mpaiva/gol-cam/.plans/session-2026-06-04.md

# Session Summary — 2026-06-04

## Prompts (in order)
1. *"create a plan to add the cam calibration to the display"*
2. *"implement option b"*
3. *"update the session summary"*

## What shipped

### Plan: cam calibration on the HMI display
- **`abe38cf`** — `.plans/cam-calibration-on-hmi.md`. Three UX
  options (A: enhanced side-status pill; B: calibration overlay
  covering the score area; C: full calibration snapshot with JPEG
  decode), with cost/risk and a recommended phasing A → B → defer C.

### Option B: full calibration overlay on the HMI
Implemented over 4 commits as user-feedback drove the UI from a
small panel up to a full-screen modal that repaints the placar
cleanly on dismiss:

- **`1b36d56`** — Option B baseline. `CamState` gained
  `motionTh`, `colorTh`, `calContrast`, `hasCalSnap`, and a 40-byte
  `calMsg`. New `extractStringField()` helper mirrors the existing
  `extractIntField` / `extractBoolField` JSON parsers. New
  `CalOverlay` struct + state machine
  (`RUNNING → RESULT_OK/FAIL → OFF`). `drawCalOverlay()` renders
  title / live `calMsg` / 3-stop progress bar / Cancelar button. Cam
  state transitions (`1 → 0`) trigger the RESULT phase. `ACT_CAL_CANCEL`
  resets the cam and collapses the overlay. Touch hit-test swallows
  taps under the overlay; only Cancelar fires (returns `-2`,
  routed to `ACT_CAL_CANCEL`). 70/70 integration tests still passed.

- **`cb9fe2e`** — polish: `calMsg` buffer bumped 40 → 64 bytes (the
  cam's full failure message is ~61 chars), added a raise-time
  snapshot of `calMsg` plus a 500 ms min-age gate so a stale FAILED
  message from the previous attempt no longer flips the overlay to
  RESULT_FAIL on frame 1 (this was the entire "neither change took"
  user feedback), and rewrote the panel as solid white fillRect (no
  rounded corners) with strong blue text — eliminates corner
  bleed-through. Result phase keeps green/red title colour-coding;
  Cancelar keeps red bg + white text.

- **`a33cb2e`** — overlay is now full-screen (800 × 480) and all
  underlay redraws are gated by `!overlayActive()`. Without this,
  `pollCam`'s `dirtyButtons` flag would punch the green START rect
  through the white overlay (the screenshot that showed "START
  visible inside the white panel"). Same gate on the touch-release
  drawButton(prev/btn) in `serviceTouch()`. Title bumped to text
  size 4 for the bigger canvas, layout reflowed around the new
  dimensions, dismiss path sets `dirtyHeader` too since the header
  is now also under the overlay.

- **`dcb85b7`** — dismiss path now calls `renderFull()` directly
  instead of relying on the loop's per-flag redraws. The loop's
  `dirtyButtons` handler is hard-coded to repaint only button index
  5 (START, the only one whose label changes via pollCam), so
  dismissing the full-screen overlay left the other 7 placar
  buttons white-on-white. Both dismiss paths (state-machine
  auto-dismiss after 3 s and `ACT_CAL_CANCEL`) now do a full
  fillScreen + drawHeader + drawScoreDigits + drawButtons (all 8)
  + drawSideStatus. Added a forward declaration for `renderFull()`.

### Calibration plan updated
- **`abe38cf`** + (next: needs Option B status update). Mark Option
  B as **DONE** in `.plans/cam-calibration-on-hmi.md`.

## What did NOT ship (yet)
- **Option A** (the cheaper enhanced side-status pill from the
  same plan). Skipped because the user wanted Option B directly,
  and Option B effectively subsumes A — the live `calMsg`,
  thresholds, and result feedback all show up in the overlay.
- **Option C** (full calibration snapshot via JPEG decode).
  Deferred per the original plan.
- **The HMI WebServer-lockup follow-up** from 2026-06-03 was
  closed as part of yesterday's session (`77ec6ec` ported to
  `esp_http_server`, `651b116` made the test runner keep-alive
  per host). Verified 70/70 today as a regression check after the
  baseline overlay landed.

## Bugs discovered + fixed during user-testing
| # | Symptom | Root cause | Fix |
|---|---|---|---|
| 1 | `calMsg` truncated to "Place dadi" | 40-byte buffer too small | Bump to 64 bytes (cb9fe2e) |
| 2 | Title said "Calibrando" with a FAILED message under it | Cam stays in state=1 for a beat after writing the failure to calMsg | Detect FAILED/FALHOU prefix in calMsg and flip to RESULT_FAIL early (cb9fe2e) |
| 3 | Early-fail flipped on frame 1 | Stale calMsg from the previous attempt was already present | Snapshot calMsg at CAL-tap time + 500 ms min-age gate (cb9fe2e) |
| 4 | "Memory issue with the display" — dark overlay had artifacts | Rounded corners exposed underlying score view through transparent radii | Solid white fillRect + blue text, no rounded corners (cb9fe2e) |
| 5 | Green START leaking through white overlay | `dirtyButtons` from pollCam triggered `drawButton(5)` while overlay was up | Gate the underlay redraws by `!overlayActive()` (a33cb2e) |
| 6 | User expected full-screen overlay | Overlay was 780 × 335, header + side-status visible in black around it | Switch to 800 × 480 + gate dirtyHeader + dirtyStatus too (a33cb2e) |
| 7 | Placar came back "stripped" after overlay dismissed | Loop's dirtyButtons handler only redraws button index 5 (START) | Call `renderFull()` directly in both dismiss paths (dcb85b7) |

## Verification
- `python3 tests/integration/test_system.py` → **70/70 green** after
  the Option B baseline (1b36d56). Not re-run after every polish
  commit since the polish was UI-only (no REST surface changed).
- User-visual confirmation at each iteration via `/remote-control`
  screenshots.

## Commit list this session
- `abe38cf` — docs: cam-calibration plan
- `1b36d56` — hmi: calibration overlay (Option B baseline)
- `cb9fe2e` — hmi: overlay polish (64-byte buffer, raise-time gate, white panel)
- `a33cb2e` — hmi: full-screen overlay + all-layer gating
- `dcb85b7` — hmi: renderFull() on dismiss

All pushed to `origin/master`. Tree clean. Branches in sync.

## Pickup list for next session

1. **Test the calibration overlay during an actual partida.**
   The flow has been verified statically — tap CAL A, see overlay,
   see calMsg/progress, RESULT phase, dismiss to clean placar. Real
   referee usage during a match will surface anything we missed:
   - Does the operator hit Cancelar before they meant to?
   - Is the 3 s RESULT phase the right duration?
   - Do they want to see the cam's calMsg in the FAIL result page
     (currently we show the generic "Sem dadinho detectado /
     Posicione e toque CAL novamente" instead)?
2. **Camera B intermittent dropouts.** Still happening from
   yesterday's session — cam B at `192.168.40.91` goes offline
   periodically. Either a hardware issue (power, cable) or a
   firmware-level WiFi/HTTP server problem. Test by leaving cam B
   running for an hour and watching `/status` via curl. If it
   reliably drops, capture serial during the drop.
3. **Retire the LED MAX7219 placar.** With the HMI fully working
   as the placar + operator surface, the LED placar is no longer
   needed. Physically power it down OR keep it as a parallel mirror
   (set its IP to something other than `.89`).
4. **Option A from the cal-calibration plan is now obsolete** —
   the side-status pill enhancement was redundant with the overlay.
   Could either remove the Option A description from the plan or
   leave it as historical context. Trivial cleanup.

## How to pick up cold
- `git log --oneline -10` shows all commits.
- The cal-overlay implementation lives in
  `src_hmi/main.cpp`:
  - `CamState` extensions: lines ~273-292
  - `CalOverlay` struct + constants: lines ~340-370
  - `extractStringField()`: lines ~395-410
  - `runAction()` cases for CAL_A / CAL_B / CAL_CANCEL: ~620-680
  - `drawCalOverlay()` + `updateCalOverlay()`: lines ~880-1000
  - `hitTest()` overlay route + `serviceTouch()` press-feedback
    gating: ~1010-1130
  - Main loop dirty-flag gates: ~1340-1360
  - Overlay paint at end of loop: ~1365-1370
- `curl http://192.168.40.89/debug/touch` returns chip diagnostic
  state any time.
- `python3 tests/integration/test_system.py` runs the 70-check
  REST suite. Persistent keep-alive client (651b116) means
  re-running back-to-back is safe.
- HMI serial is on `/dev/cu.usbserial-110` (was `-10` earlier in
  the session; port renumbered when the cable was replugged).

---

## Continued — 2026-06-04 (later in the day)

### Prompt
*"the screens and buttons work, but the calibration is not as
successful as the legacy method. is this because of limiting
processing power of the display board?"*

The honest answer: no — calibration runs entirely on the camera, the
HMI just sends the trigger and shows the result. The user's perceived
quality drop comes from operating blind: the cam dashboard shows a
live MJPEG with ROI overlay, the HMI showed nothing about what the cam
was actually seeing. Took two follow-up requests from there
("implement option c" → ship the static cal-snapshot preview; *"scope
[live MJPEG] as a follow-up plan"* → write the plan).

### Option C: cam-snapshot preview in the overlay (SHIPPED, commit `ae41369`)
Pulls the cam's `/cal-snapshot` JPEG into a PSRAM buffer, decodes
with TJpg_Decoder, renders into a 320×240 region of the calibration
overlay. Operator can now see what the cam was looking at and
diagnose failures ("dark image, no edges found → cam needs more
light") at a glance.

Tech notes:
- Added `bodmer/TJpg_Decoder@^1.1.0` to platformio.ini for crowpanel_hmi
  env.
- 32 KB PSRAM buffer alloc'd once at boot via `ps_malloc`; observed
  JPEG sizes are ~2 KB but the cam can grow larger for textured
  scenes.
- TJpgDec callback receives ABSOLUTE screen coords (already offset
  by what was passed to `drawJpg(SNAP_X, SNAP_Y)`), so the callback
  passes `x, y` straight to `gfx->draw16bitRGBBitmap` without
  further adjustment. The first version of the callback was
  double-adding `SNAP_X + x`, putting pixels off-screen.
- Two-fetch trigger: once on overlay raise (instant preview of
  previous attempt's frame), once on state-transition to RESULT
  (refresh to THIS attempt's frame). Result phase auto-dismiss
  extended from 3 s to 6 s so the second fetch has time to
  complete and the user actually sees the new frame.
- Anti-flicker: `snapVersion` counter bumps on each successful
  fetch; `drawCalOverlay` only re-decodes the JPEG when the
  version changes since last paint. Without this gate, every
  `dirtyOverlay` tick (caused by polling, state changes, etc.)
  was re-fillRect-ing and re-decoding the snap area.
- The full-screen white background fill that opens
  `drawCalOverlay` is now done in four strips AROUND the snap
  area instead of one rect through it. Otherwise the version
  gate would refuse to re-decode, leaving the snap area white
  between fetches.

Bug journey along the way:
| # | Symptom | Root cause | Fix |
|---|---|---|---|
| 1 | Snapshot fetch never logged | User wasn't tapping CAL during my serial-capture windows; bash `echo` prompts are invisible to the user | Use AskUserQuestion to coordinate tap timing; capture in background and read the saved log after |
| 2 | `TJpgDec.drawJpg returned 1` but no image visible | Callback was double-adding SNAP_X/Y → pixels at (560+, 300+), off-screen | Pass `x, y` straight from the callback to gfx without offset |
| 3 | Image renders for first fetch, "(carregando…)" persists for second | State-transition request sets `calSnapReady=false`, drawCalOverlay paints placeholder over the image, second fetch never re-paints because result phase auto-dismissed before fetch completed | Extend result-phase timeout from 3 s to 6 s |
| 4 | Image renders but flickers heavily | Every `dirtyOverlay` tick re-fillRect'd + re-decoded the snap area, even when the JPEG hadn't changed | Add `snapVersion` counter + version-gated decode in drawCalOverlay |
| 5 | Less flicker but still some | Top-of-`drawCalOverlay` fillRect was clearing the snap area on every call; version-gate then refused to re-decode | Replace the fullscreen fillRect with 4 strips that leave the snap area untouched |

### Plan: live MJPEG preview as a follow-up (NOT SHIPPED, doc only)
- **`1416e1f`** — `.plans/live-stream-preview.md`. Three scope levels
  (A: live during overlay only — recommended; B: always-on main view;
  C: two-up side-by-side). Level A breakdown lists 5 sub-tasks each
  ~50 LOC, leans entirely on the already-shipped TJpgDec +
  version-gated redraw plumbing. Only the feed source changes from
  one-shot `/cal-snapshot` to continuous `/stream` MJPEG at 5 fps.
- Plan honestly says ESP32-S3 can't run a browser to mirror the cam's
  HTML/JS dashboard directly — the live-stream + native-button
  hybrid is the realistic answer to "can we access the cam UI from
  the display?"

### Final commit list (this session, full)
- `abe38cf` — docs: cam-calibration plan
- `1b36d56` — hmi: calibration overlay (Option B baseline)
- `cb9fe2e` — hmi: overlay polish
- `a33cb2e` — hmi: full-screen overlay + all-layer gating
- `dcb85b7` — hmi: renderFull() on dismiss
- `43923b5` — docs: earlier session summary + mark B done
- `ae41369` — hmi: cal-snapshot preview (Option C)
- `1416e1f` — docs: live-stream follow-up plan

All pushed to `origin/master`. Tree clean.

### Updated pickup list

1. **Implement Level A of `.plans/live-stream-preview.md`** — live
   MJPEG preview during the calibration overlay. Builds on top of
   the existing TJpgDec + version-gated decode plumbing; only the
   feed source changes from one-shot `/cal-snapshot` to continuous
   `/stream` at 5 fps. Closes the blind-calibration UX gap that
   was the originating concern.
2. **Camera B intermittent dropouts.** Still open from yesterday.
3. **Retire the LED MAX7219 placar.** Still applicable.
4. **Test the full overlay+snapshot flow during an actual partida.**
   The static snapshot covers the diagnostic case ("why did cal
   fail?") but not the positioning case ("is the dadinho in
   frame?"). Level A's live preview will cover positioning. Wait
   to do both real-partida tests until Level A ships.
5. **Residual snap-area flicker.** User mentioned brief flicker
   even after the version gate + 4-strip fill. Acceptable for now
   but a cached RGB565 framebuffer (~150 KB in PSRAM) would let
   us blit the decoded frame instead of re-decoding, eliminating
   the flicker entirely. Worth doing as part of Level A when we
   touch this code anyway.

### Updated "how to pick up cold"
Same as before, plus:
- TJpg_Decoder code paths in `src_hmi/main.cpp`:
  - JPEG buffer + state globals: ~lines 360-380
  - `fetchCalSnapshot()`: ~lines 730-790
  - `calSnapTjpgOutput()` (TJpgDec callback): ~lines 800-810
  - `requestCalSnapshot()` helper: ~lines 1380-1395
  - Worker integration in `workerTask()`: ~lines 1320-1355
  - Render block inside `drawCalOverlay()` with version-gate:
    ~lines 940-975
- TJpgDec lib pinned at `bodmer/TJpg_Decoder@^1.1.0` in
  `platformio.ini`.
- The 4-strip background fill at the top of `drawCalOverlay`
  preserves the snap area on each repaint — be careful not to
  re-introduce a fullscreen fillRect.
