mpaiva/gol-cam/.plans/session-2026-06-03-gt911.md

# Session Plan -- 2026-06-03 (resumed from 2026-05-26)

## Prompt
"add an explicit GT911 init sequence" — after the touch panel on the
CrowPanel HMI stopped registering touches entirely (chip alive on I²C
but config-version reg reads 0xFF and status reg stays 0x00).

## Context (what we knew going in)
- HMI board has been promoted from a passive placar mirror to the
  full-featured placar (cameras push goals to it; on-screen referee
  buttons A+/A-/B+/B- + CAL A / START / RESET / CAL B all map to local
  REST handlers).
- Touch was working at one point (RESET button responded), then went
  totally dead after the debounce thresholds were tightened.
- Symptom diagnosis: chip responds to product-ID query (`"911?"`,
  firmware `0x1060`) but config-version register (`0x8047`) reads
  `0xFF` and status register (`0x814E`) is permanently `0x00`. The
  chip has no factory config burned in, so it refuses to scan.

## Things tried that did NOT work
1. **Soft reset (command 0x02).** No effect — chip stayed in same
   no-scan state.
2. **Factory restore (command 0x05).** *Worse* — this command isn't in
   every GT911 firmware revision, and the unit responded by locking up
   its I²C bus. Every subsequent `requestFrom()` returned `Error -1`
   until power cycle. Code path has been reverted.

## What is on the chip right now (commit `4309e69`)
Inline `gt911` driver in `src_hmi/main.cpp`:

1. Probes product ID + firmware version (diagnostic).
2. Reads config version. If `0xFF` or `< 0x42`, writes a verified
   185-byte 800×480 single-touch config blob lifted from Beken's
   `armino` SDK (`middleware/driver/tp/tp_gt911.c`, the `#else`
   branch). Then writes `1` to `0x8100` to commit.
3. Puts command register in normal scan mode (`0`).
4. Clears status byte so the first touch produces a fresh "ready"
   event.
5. Polling loop reads status every ~loop iteration; on bit 7 set,
   reads 7-byte point 1 record and decodes X/Y.

The chunked-write helper (`writeRegs`) splits the 185-byte payload
into 16-byte transactions because Wire's default 128-byte buffer
can't hold the whole thing in one go.

## What to verify next session
1. **Did the config write take?** Plug in HMI, watch serial monitor
   (`pio device monitor -e crowpanel_hmi`). Expect:
   ```
   [gt911] product_id = "911?"
   [gt911] firmware = 0x1060
   [gt911] config version = 0xFF
   [gt911] no valid config — writing fallback blob
   [gt911] writing 800x480 config blob (Beken/armino, ver 0x42)
   [gt911] post-write config version = 0x42 (want 0x42)
   [gt911] init complete, polling enabled
   ```
   If `post-write config version` reads `0x42`, the chip accepted the
   config and should now scan. Touch any button — `[gt911] status=...`
   diagnostic prints every 500 polls should show non-zero values, and
   button-press handlers should fire.

2. **If I²C is still locked up from cmd 0x05:** unplug for >5 seconds
   to fully drain the panel's 3V3 rail, then replug. GT911 will reset
   to its default state.

3. **If config writes but touches still don't fire:** the
   drive/sense thresholds in the Beken blob were tuned for *their*
   800×480 panel, not the Elecrow DIS07050H. Touches may register but
   only at very high pressure, or the chip may keep reporting `status
   = 0x00` because the sensing threshold is too high. Path forward
   then is to capture the chip's behaviour via Goodix's Windows
   tuning tool, or try alternative config blobs (LovyanGFX / TouchGFX
   demos have a few).

## Tertiary follow-ups (queued, not blocking)
- **Retire the LED placar entirely.** The MAX7219 board still gets
  pushed to as a parallel mirror because the camera firmwares haven't
  been re-pointed at the HMI IP. Once touch works, change
  `SCOREBOARD_IP` on both cameras from `.89` (LED placar) to the
  HMI's IP, and unplug the LED placar.
- **Hardware reset pin.** If we ever find which GPIO on the CrowPanel
  is wired to the GT911 RST line, we can do a clean reset on each
  boot and avoid relying on "config version probe" heuristics. The
  Elecrow wiki schematic suggests GPIO 38 might be RST but it's
  unconfirmed.
- **Test suite.** `tests/integration/test_system.py` (70 checks)
  currently passes for placar + cameras. There's no touch-coverage
  test because the HMI exposes touches only via UI side effects, not
  REST. Could add a `/debug/touchcount` endpoint that returns
  `pollCount` + `touchCount` for assertions.

## Commits this session
- `1d4feb4` — hmi: explicit GT911 init sequence (probe id,
  normal-scan, log cfg ver)
- `4309e69` — hmi: write GT911 800x480 config blob when chip ships
  with blank NVRAM

## Open question for the user
Touch behaviour needs to be eyeballed on the hardware — it can't be
verified from this side. The user's next confirmation determines
whether the config-write fixed it or whether we need to chase the
RST-pin or alternate-blob paths.

---

## Update: config-write attempt confirmed FAILED at chip level (later in session)

After flashing the config-blob writer, the user said "buttons aren't
working". Pyserial-based serial capture revealed:

```
[gt911] product_id = "911?"
[gt911] firmware = 0x1060
[gt911] boot config version = 0xFF
[gt911] no valid config — writing fallback blob
[gt911] writing 800x480 config blob (Beken/armino, ver 0x42)
[gt911] post-write pre-commit readback: 42 20 03 E0 01 01 3D 00
[gt911] post-commit config version = 0xFF (want 0x42)   ← REVERTED
[gt911] init complete, polling enabled
[gt911] status=0x00 (poll #500)
[gt911] status=0x00 (poll #1000)
...
```

What we learned:
- **Writes succeed** — chip accepts and stores our 185 bytes in config
  RAM. Pre-commit readback shows `42 20 03 E0 01 01 3D 00` (the
  first 8 bytes of the Beken blob) exactly. Bus is healthy.
- **Commit silently fails** — `0x8100 ← 1` (and `0x8101 ← 1`) does NOT
  apply the config; version reverts to `0xFF`. Tried dual-commit, 50ms
  + 500ms delays, recomputed-from-source checksum (verified `0x4F`
  correct via Python). Same result every time.
- **Status reg stays `0x00` for thousands of polls** — chip is alive
  and answering I²C but is NOT in scan mode.

This is a chip-level rejection, not a firmware bug. The most plausible
explanation is that the GT911 NVRAM on this unit is in a "factory blank
+ commit-locked" state — possibly because the unit shipped with the
factory programming step skipped. Software workarounds (config-blob
writes, soft reset, factory-restore command) have all failed; one
(`cmd 0x05`) bricked the I²C bus until power cycle.

## Remaining paths forward (not attempted this session)

1. **Hardware RST pulse.** The CrowPanel must wire GT911 RST to *some*
   GPIO, we just haven't located it. Common candidates from CrowPanel
   schematics seen elsewhere: GPIO 38, 39, 42, 48. Try toggling each
   low/high pre-`Wire.begin()` and re-probe the chip — a real hardware
   reset would clear the NVRAM lock if that's what's happening.
2. **Goodix's Windows tuning tool (GoodixTool).** Connects to the chip
   over I²C from a PC and can directly burn config to NVRAM using
   protected commands not in the public datasheet. Requires either an
   I²C bridge or running the HMI in pass-through mode.
3. **Panel-side hardware fault.** If the GT911 NVRAM is genuinely dead,
   no software path recovers it. Worth pinging Elecrow support
   referencing this serial trace.
4. **Work around it.** Touch is *not* required — the HMI already serves
   the full REST API. A phone browser pointed at
   `http://192.168.40.89/` (or whatever frontend gets added later) can
   drive A+/B+/RESET/CAL just as well. Cameras still push goals here
   regardless.

## What's on the device right now (commit `<latest>`)

- `/debug/touch` exposes full chip diagnostic state as JSON:
  `prod_id`, `fw`, `boot_cfg_ver`, `post_cfg_ver`, `wrote_blob`,
  `wrote_ok`, `poll_count`, `touch_count`, `last_status`, `last_x`,
  `last_y`, `touched_now`. Curlable from a laptop.
- `/debug/gt911-rewrite` re-runs the config write on demand (handy
  while testing alternate blobs).
- Diagnostic state vars (`gt911::lastStatus`, `bootCfgVer`,
  `postCfgVer`, `wroteBlob`, `wroteOk`, etc.) tracked across boot.
- Heartbeat log every ~1.25 s (`[hb] polls=... touches=...`) so
  serial monitor can confirm whether the polling loop is even alive.

## Pickup list for next session
- **Try option (1)**: toggle GPIO 38 low for 10ms, high, sleep 50ms,
  then `Wire.begin()`. Test the chip's response. Repeat for 39, 42,
  48 if no joy.
- **If RST pulse changes nothing**: pivot to option (4) — accept that
  touch is dead on this CrowPanel and ship the phone-as-controller
  workflow. The HMI is still useful as a big visible score display.
- **If the user wants to try option (2)**: source an I²C-to-USB
  bridge (CP2112 or FTDI breakout in I²C mode), download GoodixTool
  from Goodix support.

---

## RESOLUTION — 2026-06-03 (later that day)

Touch is now fully working. All 8 buttons (A+/A-/B+/B-, CAL A,
START, RESET, CAL B) fire correctly. The full saga in summary:

1. **The GT911's commit machinery IS broken** — config version still
   reads `0xFF` after `0x8100` + `0x8101` writes; the chip refuses
   our blob and reverts. That part of the diagnosis was correct.
2. **The wide RST-pin sweep clobbered the RGB display** — almost
   every general-purpose GPIO on this board is wired to LCD data /
   sync lines; pinMode-as-OUTPUT on those redirects them off the
   LCD peripheral. Symptom: stuck white screen. Fix: rip out the
   sweep, power-cycle. Lesson: confirm "general-purpose" means
   general-purpose on a given board before pulsing pins.
3. **The chip is actually scanning anyway.** After the panel
   recovery, `/debug/touch` showed `touch_count: 140` with valid
   `(last_x, last_y)` even though the config version still said
   `0xFF`. The chip has SOME mode where it scans and reports
   touches via the status register even without a host-loaded
   config — possibly a hardcoded factory-default. The commit
   appears to be cosmetic; scanning runs regardless.
4. **The real bug was in OUR firmware** — the release-fire scheme
   in `serviceTouch()` required `held >= MIN_PRESS_MS (30ms)`. The
   chip reports touches as one-shot status-bit blips (not a held
   "data ready" window), so `gt911::touched` flips back to false
   between polls during a real press, the apparent "release" event
   has `held < 30ms`, and the action is silently dropped. Visual
   feedback fired (color change) but the action queue did not.
5. **Fix**: fire on press with a 250 ms cooldown. Implemented in
   commit `8f53704`. Verified: 3 taps on A+ → score = 3; all 8
   buttons confirmed working.

## Closing state
- HMI fully functional as the placar + operator surface at
  `192.168.40.89`.
- Touch reliable through the fire-on-press path.
- `/debug/touch` endpoint preserved for future GT911 debugging.
- `/debug/gt911-rewrite` preserved (harmless even if commit
  keeps reverting).
- The blob-writer code is still in begin() — harmless because the
  trigger (`if (cfgver == 0xFF)`) fires once at boot and the chip
  reverts immediately; future boards with valid factory config
  will skip the write entirely.

## Not-yet-tackled follow-ups
- Cross-check that the camera firmwares are pointing at the HMI
  for `SCOREBOARD_IP` (currently `.89`). Already match.
- Eventually retire the LED MAX7219 placar; nothing depends on it
  now that the HMI works.
- The integration test suite (`tests/integration/test_system.py`)
  exercises the REST contract — re-run after this batch of commits
  to confirm nothing regressed (it shouldn't have; we only changed
  the HMI touch dispatch, not handlers).
- **HMI WebServer lockup under burst load.** When the integration
  suite hits the HMI in tight loops (`/api/reset` + `/status`
  polled ~12×/3s during cross-board tests, several test groups
  back-to-back), port 80 starts refusing connections even though
  the device keeps polling and heartbeating on serial. Heap and
  task health look fine in the heartbeat. Suspect TCP socket pool
  exhaustion in the ESP32 Arduino `WebServer` (default 5 sockets,
  none explicitly closed by handler) or `String`-heap
  fragmentation in `sendJson()`. Workaround: soft-reset
  (DTR/RTS toggle) or power-cycle restores HTTP, then the full 70-
  test suite passes green. Real fix probably needs switching the
  HMI from `WebServer.h` to `esp_http_server` (the same stack the
  cameras use), or adding an explicit `WiFiClient::stop()` /
  `flush` in handlers, or trimming `String` use in JSON builders.

---

## Session wrap-up — 2026-06-03

### Verification done after the touch fix
- `python3 tests/integration/test_system.py` → **70/70 green** on a
  fresh HMI boot. Covers placar `/status` shape, both cameras'
  `/status`, `/reset`, `/deduct` clamp, `/calibrate` transitions,
  and the cross-board paths (`/test-goal`, `/test-fire`, VAR-annul
  sync via `/goal-undo`).
- Note: a second consecutive suite run failed 8 cross-board tests
  because the HMI's WebServer locked up (the follow-up logged
  above). Soft-reset + re-run = green again. Reproducibly
  triggered by the burst load.

### README update
- `README.md` rewritten to describe **three boards** instead of two
  (camera + LED placar + CrowPanel HMI). New BOM entry for the
  HMI, three-env build commands, autonomous-placar section
  mentioning both placar variants, and a new Tests section pointing
  at `tests/integration/test_system.py`. Commit `03f97cd`.

### Final commit list this session (10 commits, `feee99f..03f97cd`)
1. `1d4feb4` — hmi: explicit GT911 init sequence
2. `4309e69` — hmi: write GT911 800×480 config blob (later proved
   cosmetic — chip rejects commit, but harmless)
3. `a8278e6` — docs: initial session plan
4. `1f2ad98` — hmi: `/debug/touch` + `/debug/gt911-rewrite` endpoints
5. `3980561` — docs: chip-level GT911 commit-rejection finding
6. `0db97a1` — hmi: stop sweeping RGB-display GPIOs (white-screen fix)
7. **`8f53704` — hmi: fire touch actions on press (THE actual fix)**
8. `010edf9` — docs: GT911 saga resolution
9. `0b2fe30` — docs: HMI WebServer-lockup follow-up
10. `03f97cd` — docs(readme): add CrowPanel HMI as third board

All 10 pushed to `origin/master`. Tree clean.

## Pickup list for next session (in priority order)
1. ~~**Reproduce + fix HMI WebServer lockup under burst load**~~ —
   **DONE in commit `77ec6ec`.** Ported the HMI's 11 REST handlers
   from `WebServer.h` to `esp_http_server` (same stack the cameras
   use, with `max_open_sockets=10` + `lru_purge_enable=true`).
   Also rewrote handlers to be no-String (snprintf into stack
   buffers) so heap doesn't fragment over time. Verified by
   running `test_system.py` 3× back-to-back: port 80 is fully
   responsive between runs, no power-cycle needed. Intermittent
   cross-suite failures during verification traced to camera B
   going offline mid-test, not the HMI.
2. **Camera B intermittent dropouts.** Cam B (`192.168.40.91`)
   was unreachable for stretches during the HMI verification.
   `test_system.py` crashes with `AttributeError: 'NoneType'`
   when a camera passes the initial reachability gate but goes
   offline mid-test. Worth (a) hardening the test runner to
   skip a suite when a per-test fetch returns None, and (b)
   investigating cam B's WiFi stability / power supply.
3. **Retire the LED MAX7219 placar.** Nothing depends on it now
   that the HMI is the source of truth at `.89`. Either physically
   power it down or de-prioritize building/flashing it. The repo
   keeps the firmware as a reference / fallback option.
3. **Goodix tuning** — the GT911 commit-revert ("post_cfg_ver:
   0xFF") still bugs me. Now that touch works in practice, this is
   purely "would be nice to know why." Could be a low-priority
   weekend rabbit hole with an I²C-USB bridge + GoodixTool.
4. **Stress test the HMI as the standalone placar** during an
   actual partida. Validate buttons, UI feedback, calibration
   flow, and whether the WebServer-lockup happens organically (vs
   only under synthetic test load).

## How to pick up cold
- `git log --oneline -10` shows the session's commits.
- Open `src_hmi/main.cpp` and read `serviceTouch()` (around line
  704) — that's the fire-on-press implementation. Comments inside
  explain why the release-fire model failed.
- `curl http://192.168.40.89/debug/touch` returns chip diagnostic
  state any time the HMI is reachable.
- `python3 tests/integration/test_system.py` runs the full 70-check
  REST suite. Skips any board that's offline.
- `pio device monitor -e crowpanel_hmi --baud 115200` watches HMI
  serial (note: miniterm requires a real TTY; use the
  `python3 -c "import serial; ..."` snippets in the session
  history if running through a non-TTY shell).
