mpaiva/gol-cam/.plans/session-2026-03-12.md

# Session Plan -- 2026-03-12

## Completed This Session
- Researched the history of "futebol de botao" (button football) in Rio de Janeiro, Brazil
- Investigated the Dadinho variant (small cube/dice used as ball instead of flat disc)
- Compiled comprehensive research report covering origins, rules, cultural significance, and competitive structure
- Sources consulted: CBFM official website (confederacao brasileira de futebol de mesa), multiple web sources

## Key Findings
- Dadinho was officially recognized by CBFM in 2010 as the newest rule variant
- Rio de Janeiro originated the "Regra Carioca" (3 Toques) and has nearly 50 years of state championship history
- The dadinho is a small cube (~6mm per face, 0.1-0.3g) used as the ball
- Rules: 3-touch individual limit, 9-touch team limit, mandatory shot by 9th touch
- Active competitive scene with 16+ years of national championships

## Output Files
- /Users/mp/_git-repos/gol-cam/.reports/futebol-de-botao-research.md

## Next Steps / Recommendations
- If building a digital version: the dadinho's cubic physics would be the key differentiator
- Research potential for AR/camera-based gameplay (aligns with "gol-cam" project name)
- Consider interviewing Carioca button football players for authentic cultural details
- Look into the official CBFM dadinho rulebook PDF for exact specifications
- Explore the artisanal button-making tradition as potential visual design inspiration
