mpaiva/gol-cam/hardware/arquivos-historicos/Trave Eletronica .3mf

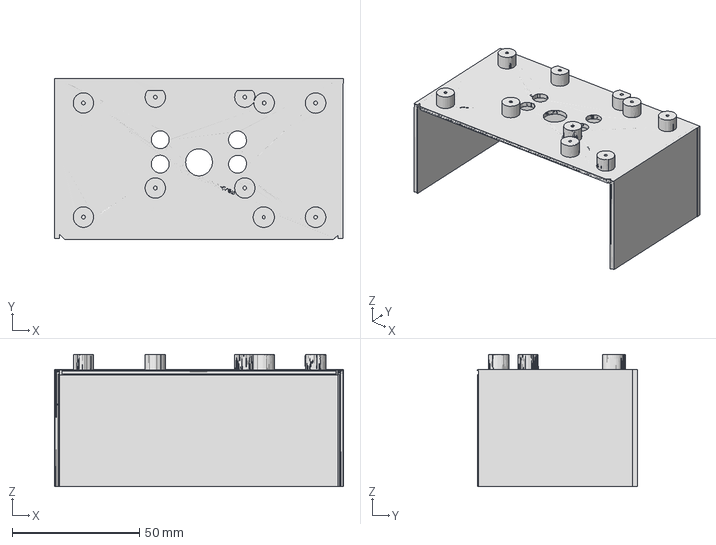
[picture p24: CAD file, 2026-05-26]
hardware/arquivos-historicos/Trave Eletronica .3mf
113.5 x 63.2 x 51.9 mm
