mpaiva/gol-cam/hardware/arquivos-historicos/Caixa Camera Golll V2.3mf

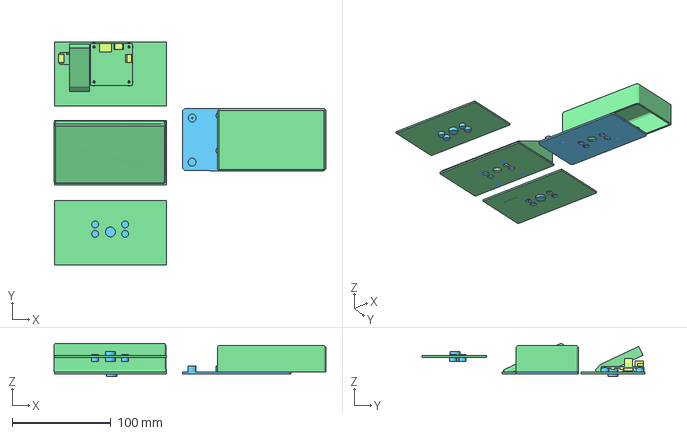
[picture p25: CAD file, 2026-05-26, an earlier design]
hardware/arquivos-historicos/Caixa Camera Golll V2.3mf
276.2 x 226.2 x 33.8 mm
