mpaiva/gol-cam/hardware/caixa-camera/Caixa Camera Golll V5.1.3mf

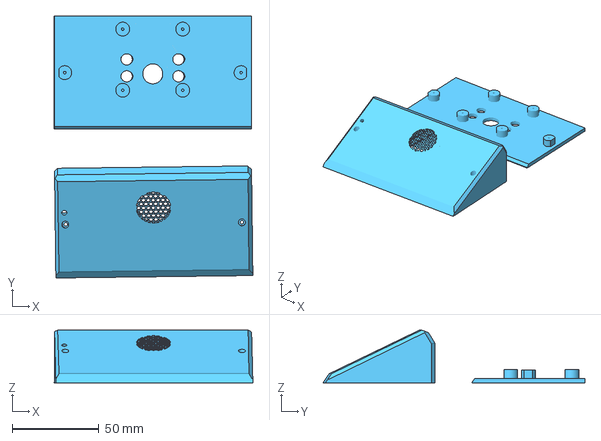
[picture p26: CAD file, 2026-05-26, an earlier design]
hardware/caixa-camera/Caixa Camera Golll V5.1.3mf
114.8 x 151.3 x 30.5 mm
