mpaiva/gol-cam/include/camera.h

#pragma once

#include "esp_camera.h"
#include "pins.h"

// Initialize OV3660 camera with given resolution and pixel format
bool initCamera(framesize_t frameSize = FRAMESIZE_QVGA,
                pixformat_t pixelFormat = PIXFORMAT_GRAYSCALE) {
    camera_config_t config;
    config.ledc_channel = LEDC_CHANNEL_0;
    config.ledc_timer = LEDC_TIMER_0;
    config.pin_d0 = CAM_PIN_D0;
    config.pin_d1 = CAM_PIN_D1;
    config.pin_d2 = CAM_PIN_D2;
    config.pin_d3 = CAM_PIN_D3;
    config.pin_d4 = CAM_PIN_D4;
    config.pin_d5 = CAM_PIN_D5;
    config.pin_d6 = CAM_PIN_D6;
    config.pin_d7 = CAM_PIN_D7;
    config.pin_xclk = CAM_PIN_XCLK;
    config.pin_pclk = CAM_PIN_PCLK;
    config.pin_vsync = CAM_PIN_VSYNC;
    config.pin_href = CAM_PIN_HREF;
    config.pin_sccb_sda = CAM_PIN_SIOD;
    config.pin_sccb_scl = CAM_PIN_SIOC;
    config.pin_pwdn = CAM_PIN_PWDN;
    config.pin_reset = CAM_PIN_RESET;
    config.xclk_freq_hz = 20000000;
    config.frame_size = frameSize;
    config.pixel_format = pixelFormat;
    config.grab_mode = CAMERA_GRAB_LATEST;
    config.fb_location = CAMERA_FB_IN_PSRAM;
    config.jpeg_quality = 12;
    // 3 framebuffers in PSRAM (~230 KB) so the camera DMA never overflows
    // when the loop pauses briefly (autotune, JPEG encoding spikes, etc).
    // CAMERA_GRAB_LATEST drops oldest frames if all buffers are full so the
    // detection loop always works with a fresh frame.
    config.fb_count = 3;

    esp_err_t err = esp_camera_init(&config);
    if (err != ESP_OK) {
        Serial.printf("Camera init failed: 0x%x\n", err);
        return false;
    }

    // OV3660-specific adjustments
    sensor_t *s = esp_camera_sensor_get();
    if (s->id.PID == OV3660_PID) {
        s->set_vflip(s, 1);
        s->set_brightness(s, 1);
    }

    Serial.println("Camera initialized OK");
    return true;
}
